Ownasaurus/TAStm32/Images/case_v3 2.png

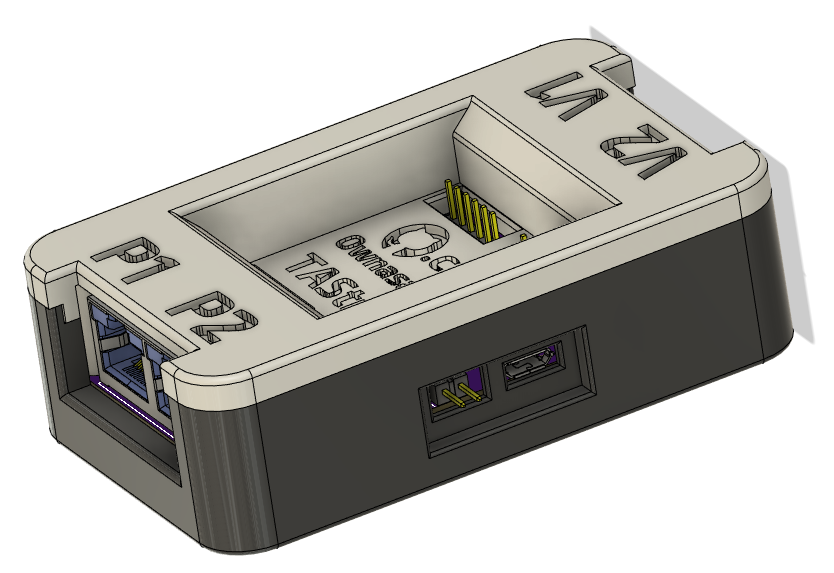
Images/case_v3 2.png
