Ownasaurus/TAStm32/Images/case_v3.png

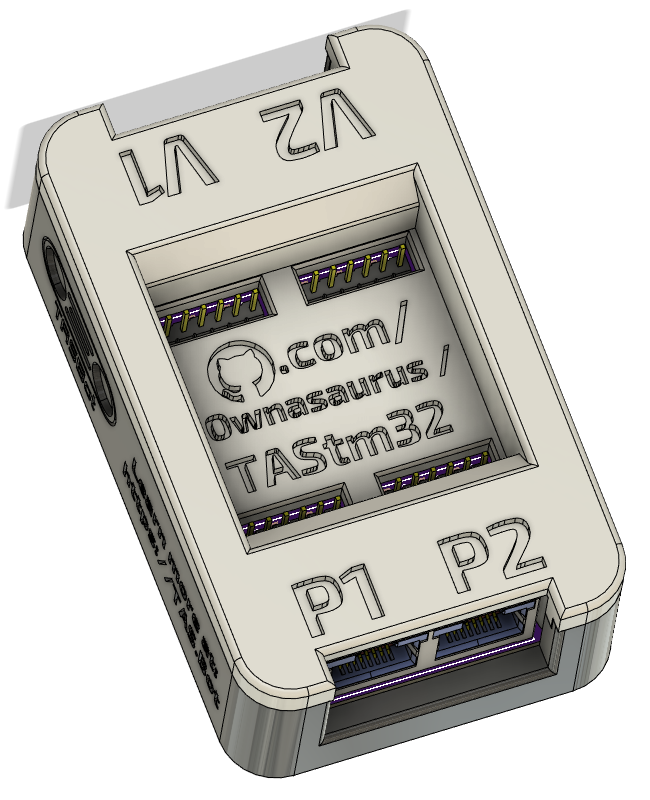
Images/case_v3.png
