Ownasaurus/TAStm32/Images/hardware_pinmaps/hardware.png

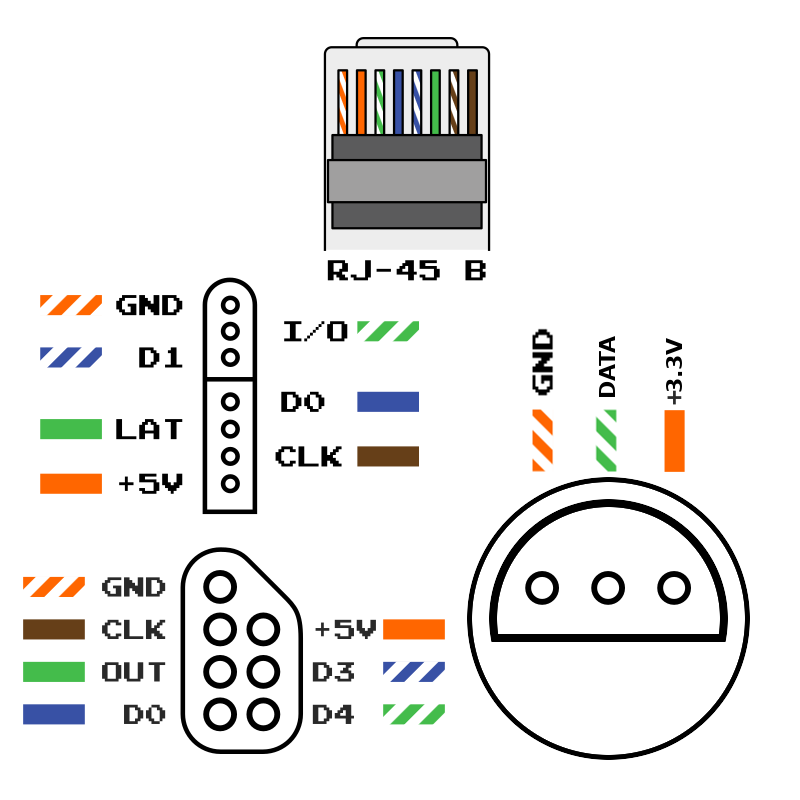
Images/hardware_pinmaps/hardware.png
