Ownasaurus/TAStm32/Images/hardware_pinmaps/hardware_genesis_v2.png

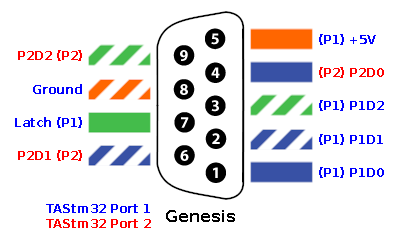
Images/hardware_pinmaps/hardware_genesis_v2.png
