Ownasaurus/TAStm32/Images/hardware_pinmaps/hardware_n64_v2.png

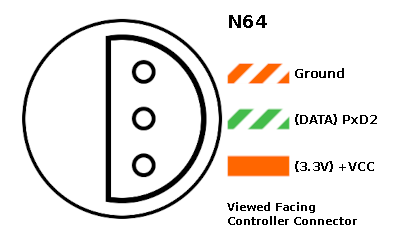
Images/hardware_pinmaps/hardware_n64_v2.png
