Ownasaurus/TAStm32/Images/pcb_v3.png

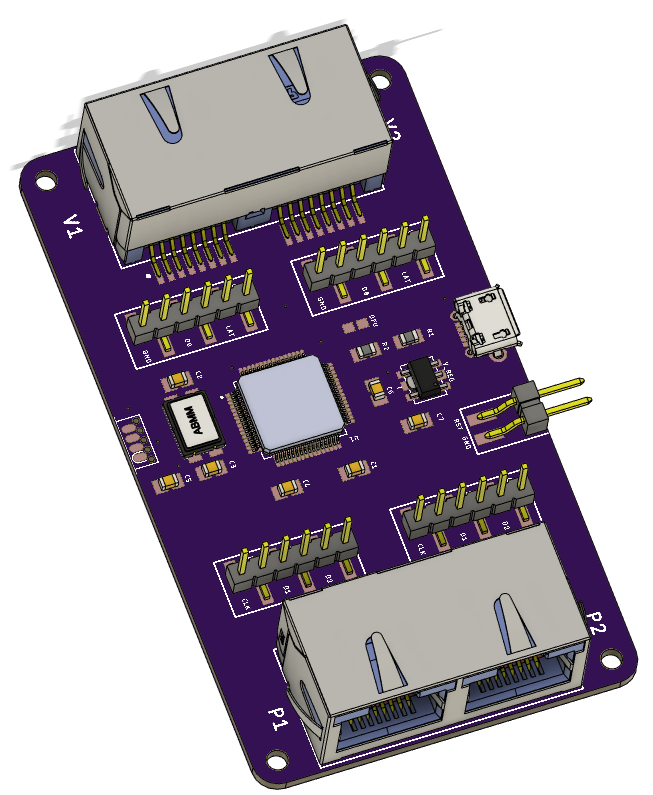
Images/pcb_v3.png
