Ownasaurus/TAStm32/Images/pinmap.png

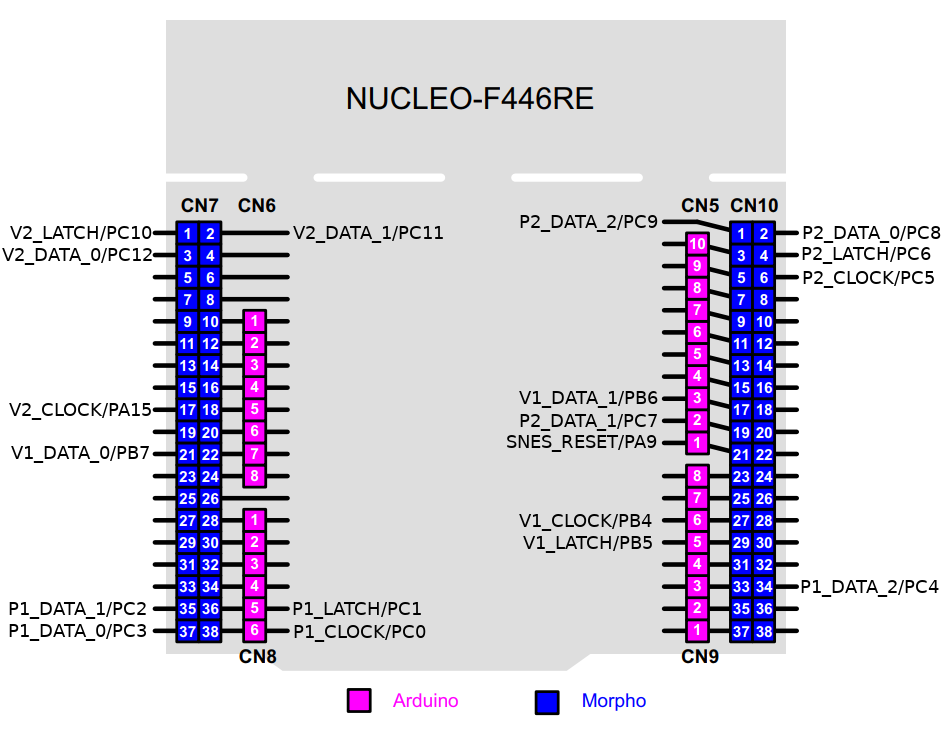
Images/pinmap.png
