Ownasaurus/TAStm32/Images/Render1.png

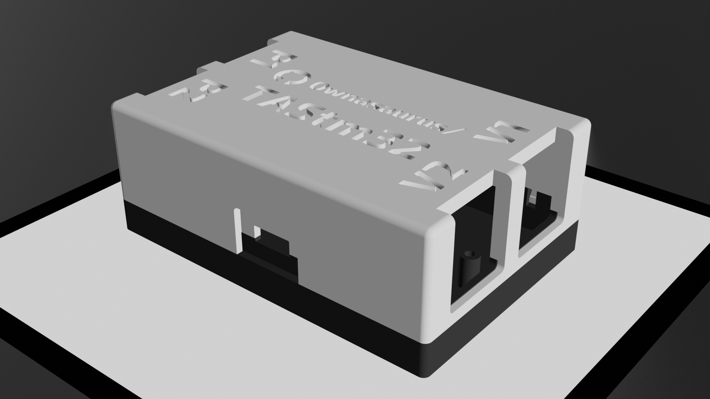
Images/Render1.png
