Ownasaurus/TAStm32/Images/Render3.png

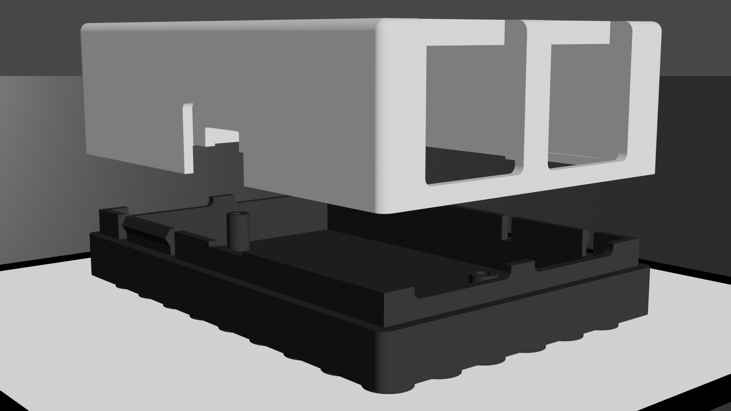
Images/Render3.png
